venari/timelapse/scripts/savePhotos.py

import subprocess
import json
from picamera2 import Picamera2, Preview
from libcamera import Transform, controls
import os
import time
import shutil
import datetime
import sys
import requests
import logging
import pathlib

# from helpers import flashLED
from helpers import currentPhase, internet
from uploadPending import uploadPhoto

config = json.load(open(pathlib.Path(__file__).parent / 'config.json'))

formatter = logging.Formatter('%(asctime)s %(name)s %(levelname)s %(message)s')
handler = logging.StreamHandler(sys.stderr)
handler.setFormatter(formatter)
logger = logging.getLogger("savePhotos")
logger.addHandler(handler)
logger.setLevel(logging.DEBUG)

logger.info("Starting up savePhotos.py...")
# os.chmod(logFilePath, 0o777) # Make sure pijuice user script can write to log file.

def reloadConfig():
    global config
    config = json.load(open(pathlib.Path(__file__).parent / 'config.json'))
    # Load the local config if it exists
    try:
        with open(pathlib.Path(__file__).parent / 'config.local.json', 'r') as f:
            local_config = json.load(f)

        # logger.info("config.local.json found. Using local config.")
        # logger.info(config)
        # Update the primary config with overrides from the local config
        config.update(local_config)
        # logger.info(config)

        # Update the primary config with overrides from the local config
        config.update(local_config)
    except FileNotFoundError:
        logger.debug("config.local.json not found. Using default config.")

reloadConfig()

## clock
#while not os.path.exists('/dev/i2c-1'):
#    time.sleep(0.1)

outputImageFolder = str(pathlib.Path(__file__).parent / '../output/images/')
workingImageFolder = os.path.join(outputImageFolder , 'working/')
pendingImageFolder = os.path.join(outputImageFolder , 'pending/')
uploadedImageFolder = os.path.join(outputImageFolder , 'uploaded/')


def getSerialNumber():
  # Extract serial from cpuinfo file
  cpuserial = "0000000000000000"
  try:
    f = open('/proc/cpuinfo','r')
    for line in f:
      if line[0:6]=='Serial':
        cpuserial = line[10:26]
    f.close()
  except:
    cpuserial = "ERROR000000000"

  return cpuserial

serialNumber = getSerialNumber()

def savePhotos():
    os.makedirs(outputImageFolder, exist_ok = True)
    os.makedirs(pendingImageFolder, exist_ok = True)
    os.makedirs(workingImageFolder, exist_ok = True)
    # txtTime = datetime.datetime.now().strftime('%Y-%m-%d %H:%M:%S')

    try:
        #with Picamera2() as camera:

        #    while True:
        while True:
            logger.debug('creating camera object...')
            with Picamera2() as camera:

                reloadConfig()
                #camera_config = camera.create_preview_configuration()
                camera_config = camera.create_still_configuration()
                
                camera.set_logging(Picamera2.ERROR) # Stop stderr/stdoutput getting filled with camera logging messages

                # # Use sensor mode 2 to give greater max exposure time.
                # camera_config = camera.create_still_configuration(raw = picam2.sensor_modes[2])

                # logger.info(config)
                # logger.info(config['camera.vflip'])
                # logger.info(config['camera.hflip'])

                camera_config["transform"] = Transform(vflip = config['camera.vflip'], hflip = config['camera.hflip'])
                camera_config["size"] = (config['camera.resolution.width'], config['camera.resolution.height'])
                # logger.debug(camera_config["size"])

                focus_m = config['camera.focus_m']

                logger.debug('focus_m is ' + str(focus_m))

                if(focus_m < 0.1):
                    focus_m = 0.1
                
                if(focus_m > 100):
                    focus_m = 100

                lensposition = 1/focus_m

                logger.debug('setting lens position to ' + str(lensposition))

                # camera.rotation = config['camera.rotation']
                camera.configure(camera_config)

                phase = currentPhase(datetime.datetime.now(datetime.timezone.utc))
                logger.debug('current phase is ' + phase)

                camera.set_controls({"AfMode": controls.AfModeEnum.Manual, "LensPosition": lensposition, "AeExposureMode": controls.AeExposureModeEnum.Normal})

                if(config["camera.enable_long_exposure_at_night"]):                    
                    if(phase == "sunset" or phase == "dawn"):
                        logger.debug('setting camera to long exposure for ' + phase)
                        camera.set_controls({"AfMode": controls.AfModeEnum.Manual, "LensPosition": lensposition, "AeExposureMode": controls.AeExposureModeEnum.Long}) 

                    if(phase == "dusk" or phase == "nautical_dusk" or phase == "night" or phase == "night_end" or phase == "nautical_dawn"):
                        logger.debug('setting camera to super long exposure for ' + phase)
                        camera.set_controls({"AfMode": controls.AfModeEnum.Manual, "LensPosition": lensposition, "ExposureTime": config['camera.long_exposure_time'], "AnalogueGain": config['camera.analogue_gain']})

                # if(config['camera.long_exposure_mode']):
                #     # camera.set_controls({"AfMode": controls.AfModeEnum.Manual, "LensPosition": lensposition, "AeEnable": False, "ExposureTime": config['camera.long_exposure_time'], "AnalogueGain": config['camera.analogue_gain']}) #, "ColourGains": (2, 1.81)})
                #     # camera.set_controls({"AfMode": controls.AfModeEnum.Manual, "LensPosition": lensposition, "ExposureTime": config['camera.long_exposure_time'], "AnalogueGain": config['camera.analogue_gain']})
                    
                #     #imx708 now has long exposure mode in tuning file
                #     camera.set_controls({"AfMode": controls.AfModeEnum.Manual, "LensPosition": lensposition, "AeExposureMode": controls.AeExposureModeEnum.Long}) 
                # else:
                #     camera.set_controls({"AfMode": controls.AfModeEnum.Manual, "LensPosition": lensposition})
                    
                camera.options["quality"] = config['camera.quality']

                # flashLED(pj, 'D2', 200, 255, 255, 1, 0.5)
                logger.debug('beginning capture')
                #camera.start_preview(Preview.DRM)
                camera.start()
                # Camera warm-up time
                logger.debug('warming up camera...')
                time.sleep(5)
                logger.debug('ready')

                IMAGEFILENAME = workingImageFolder + datetime.datetime.now().strftime('%Y-%m-%d_%H%M%S.jpg')
                camera.capture_file(IMAGEFILENAME)
                logger.debug('image saved to working folder')
                pendingFilename = pendingImageFolder + pathlib.Path(IMAGEFILENAME).name
                shutil.move(IMAGEFILENAME, pendingFilename)
                logger.debug('image moved to pending folder')
                
                # Try to upload immediately if connected to internet
                if internet():
                    logger.debug('connected to internet - attempting immediate upload')
                    try:
                        uploadPhoto(pendingFilename)
                    except Exception as e:
                        logger.warning(f'immediate upload failed: {e}')
                        logger.debug('will retry via uploadPending.py later')

            logger.debug('destroying camera object')
            

            if config['shutdown']:
                break
            else:
                if config['monitoringMode']:
                    logger.debug('monitoring mode is true, so no capture delay....')
                else:
                    time.sleep(config['camera.interval'])

    except Exception as e:
        logger.error("SavePhoto() failed.")
        logger.error(e)


def main():
    """Main entry point for savePhotos script."""
    try:
        logger.info('In savePhotos.py')

        while True:
            savePhotos()

            if not config['shutdown']:
                logger.warning("Bailed out of savePhotos() - let's pause to catch our breath...")
                # If we get here something went wrong. Let's pause for a bit and try again.
                time.sleep(30)
                
    except Exception as e:
        logger.error("Catastrophic failure.")
        logger.error(e)


if __name__ == "__main__":
    main()
