venari/timelapse/scripts/coreScript.py

import subprocess
import json
import pijuice
from picamera import PiCamera
import os
import time
import shutil
import datetime
import sys
import requests
import logging

config = json.load(open('config.json'))
logFilePath = config["logFilePath"]
os.makedirs(os.path.dirname(logFilePath), exist_ok=True)

logging.basicConfig(filename=logFilePath,
                    format='%(asctime)s %(levelname)s: %(message)s',
                    level = logging.DEBUG
                    # datefmt='%d/%m/%Y %I:%M:%S %p'
                    # encoding='utf-8'
                    )
# log = logging.getLogger()
logging.info("Starting up coreScript.py...")

# clock
while not os.path.exists('/dev/i2c-1'):
    time.sleep(0.1)

outputImageFolder = '../output/images/'
pendingImageFolder = outputImageFolder + 'pending/'
uploadedImageFolder = outputImageFolder + 'uploaded/'

outputTelemetryFolder = '../output/telemetry/'
pendingTelemetryFolder = outputTelemetryFolder + 'pending/'
uploadedTelemetryFolder = outputTelemetryFolder + 'uploaded/'

# pijuice
pj = pijuice.PiJuice(1, 0x14)

def getSerialNumber():
  # Extract serial from cpuinfo file
  cpuserial = "0000000000000000"
  try:
    f = open('/proc/cpuinfo','r')
    for line in f:
      if line[0:6]=='Serial':
        cpuserial = line[10:26]
    f.close()
  except:
    cpuserial = "ERROR000000000"

  return cpuserial

serialNumber = getSerialNumber()

def scheduleShutdown():
    alarmObj = {}

    # print(str(datetime.datetime.now()) + ' scheduleShutdown')
    logging.debug('scheduleShutdown')
    setAlarm = False

    config = json.load(open('config.json'))

    if config['shutdown']:
        # print(str(datetime.datetime.now()) + ' scheduling regular shutdown')
        logging.info('scheduling regular shutdown')
        DELTA_MIN=10

        alarmObj = {
                'year': 'EVERY_YEAR',
                'month': 'EVERY_MONTH',
                'day': 'EVERY_DAY',
                'hour': 'EVERY_HOUR',
                'minute_period': DELTA_MIN,
                'second': 0,
        }

        setAlarm = True

    # if datetime.datetime.now().hour >=18 or datetime.datetime.now().hour <= 7:
    if datetime.datetime.now().hour >=20 or datetime.datetime.now().hour <= 6:
        logging.info("Night time so we're scheduling shutdown")

        alarmObj = {
            'year': 'EVERY_YEAR',
            'month': 'EVERY_MONTH',
            'day': 'EVERY_DAY',
            # 'hour': 20, # 8am
            # 'minute_period': DELTA_MIN,
            'hour': 'EVERY_HOUR',
            'minute': 0,
            'second': 0,
        }

        setAlarm = True

    if setAlarm == True:
        logging.info("scheduleShutdown - we're setting the shutdown...")

        alarmSet = False
        while alarmSet == False:
            status = pj.rtcAlarm.SetAlarm(alarmObj)

            if status['error'] != 'NO_ERROR':
                logging.error('Cannot set alarm\n')
                # sys.exit()
                alarmSet = False
                logging.info('Sleeping and retrying...\n')
                time.sleep(10)
            else:
                logging.debug('Alarm set for ' + str(pj.rtcAlarm.GetAlarm()))
                alarmSet = True

        # Ensure Wake up alarm is actually enabled!
        wakeUpEnabled = False
        while wakeUpEnabled == False:

            status = pj.rtcAlarm.SetWakeupEnabled(True)

            if status['error'] != 'NO_ERROR':
                logging.error('Cannot enable wakeup\n')
                # sys.exit()
                wakeUpEnabled = False
                logging.info('Sleeping and retrying for wakeup...\n')
                time.sleep(10)
            else:
                logging.debug('Alarm set for ' + str(pj.rtcAlarm.GetAlarm()))
                wakeUpEnabled = True

        logging.info('Shutting down...')
        subprocess.call(['sudo', 'shutdown'])
        logging.info('Power off scheduled for 30s from now')
        pj.power.SetPowerOff(30)
    else:
        logging.debug('skipping shutdown scheduling because of config.json')
        # Ensure Wake up alarm is *not* enabled - or it will cause pi to reboot
        status = pj.rtcAlarm.SetWakeupEnabled(False)


def savePhotos():
    os.makedirs(outputImageFolder, exist_ok = True)
    os.makedirs(pendingImageFolder, exist_ok = True)
    # txtTime = datetime.datetime.now().strftime('%Y-%m-%d %H:%M:%S')

    try:
        logging.debug('creating camera object...')
        with PiCamera() as camera:

            while True:
                config = json.load(open('config.json'))
                camera.vflip = config['camera.vflip']
                camera.hflip = config['camera.hflip']
                camera.resolution = (config['camera.resolution.width'], config['camera.resolution.height'])
                camera.rotation = config['camera.rotation']

                logging.debug('beginning capture')
                camera.start_preview()
                # Camera warm-up time
                logging.debug('warming up camera...')
                time.sleep(5)
                logging.debug('ready')

                IMAGEFILENAME = pendingImageFolder + datetime.datetime.now().strftime('%Y-%m-%d_%H%M%S.jpg')
                camera.capture(IMAGEFILENAME)
                logging.debug('image saved')

                saveTelemetry()
                scheduleShutdown()
                if config['shutdown']:
                    break
                else:
                    time.sleep(config['camera.interval'])

    except Exception as e:
        logging.error("SavePhoto() failed.")
        logging.error(e)

def saveTelemetry():
    try:
        warningTemp = 50
        api_data = {
                    'batteryPercent': pj.status.GetChargeLevel()['data'],
                    'temperatureC': pj.status.GetBatteryTemperature()['data'],
                    'diskSpaceFree': shutil.disk_usage('/')[2] // (1024**3), # shutil.disk_usage returns tuple of (total, used, free), converted to int gb
                    'pendingImages': len(os.listdir(pendingImageFolder)),
                    'uploadedImages': len(os.listdir(uploadedImageFolder)),
                    'pendingTelemetry': len(os.listdir(pendingTelemetryFolder)),
                    'uploadedTelemetry': len(os.listdir(uploadedTelemetryFolder)),
                    'uptimeSeconds': int(time.clock_gettime(time.CLOCK_BOOTTIME)),
                    'status': str({ 'status': pj.status.GetStatus()['data'],
                                'batteryVoltage': pj.status.GetBatteryVoltage()['data'],
                                'batteryCurrent': pj.status.GetBatteryCurrent()['data'],
                                'ioVoltage': pj.status.GetIoVoltage()['data'],
                                'ioCurrent': pj.status.GetIoCurrent()['data']
                            }),
                    # 'Timestamp': datetime.datetime.now().astimezone().isoformat(),
                    'SerialNumber': serialNumber
                }

        telemetryFilename = pendingTelemetryFolder + datetime.datetime.now().strftime('%Y-%m-%d_%H%M%S.json')
        with open(telemetryFilename, 'w') as outfile:
            json.dump(api_data, outfile)
            logging.debug('telemetry saved')

    except Exception as e:
        logging.error("saveTelemetry() failed.")
        logging.error(e)


try:
    logging.debug('setting sys clock from RTC...')
    subprocess.call(['sudo', 'hwclock', '--hctosys'])
    logging.debug("sudo hwclock --hctosys succeeded")
except Exception as e:
    logging.error("sudo hwclock --hctosys failed")
    logging.error(e)
    

try:
    logging.info('In coreScript.py')
    if config['shutdown']:
        logging.info('Setting failsafe power off for 2 minutes 30 seconds from now.')
        pj.power.SetPowerOff(150)   # Fail safe turn the thing off

    # Give things a chance to settle down, and also restart savePhotos if it bails
    while True:
        time.sleep(30)
        savePhotos()
except Exception as e:
    logging.error("Catastrophic failure.")
    scheduleShutdown()
    logging.error(e)
